bartkepl/CanGnssNode/sim/LT8606.asc

C1: cap; 10µ; V=50
C2: cap; 100n; V=50
C3: cap; 100nF; V=16
C4: cap; 22µ; V=16
C5: cap; 100n; V=16
C6: cap; 1µ; V=50
C7: cap; 22p; V=16
I1: current; 3m
L1: ind; 6.8µ; Rser=1m
R1: res; 1Meg
R2: res; 184k
R3: res; 18k2
R4: res; 1Meg
R5: res; 182k
U1: LT8606
V1: voltage; 32
Named nets: 0
.tran 0 2m 1u
